urichess/chessboard/reader_zephyr/app/src/main2.c

/*
 * Copyright (c) 2017 Linaro Limited
 *
 * SPDX-License-Identifier: Apache-2.0
 */

#include <zephyr/kernel.h>
#include <zephyr/device.h>
#include <zephyr/drivers/gpio.h>
#include <zephyr/sys/printk.h>
#include <zephyr/sys/__assert.h>
#include <string.h>


#include <zephyr/devicetree.h>
#include <zephyr/drivers/adc.h>
#include <zephyr/sys/util.h>

/* size of stack area used by each thread */
#define STACKSIZE 1024

/* scheduling priority used by each thread */
#define PRIORITY 7

#define LED0_NODE DT_ALIAS(led0)

#if !DT_NODE_HAS_STATUS(LED0_NODE, okay)
#error "Unsupported board: led0 devicetree alias is not defined"
#endif


#if !DT_NODE_EXISTS(DT_PATH(zephyr_user)) || \
	!DT_NODE_HAS_PROP(DT_PATH(zephyr_user), io_channels) || \
	!DT_NODE_HAS_PROP(DT_PATH(zephyr_user), mux_gpios)
#error "Unsupported board: zephyr_user devicetree alias is not defined"
#endif

#define DT_SPEC_AND_COMMA(node_id, prop, idx) \
	ADC_DT_SPEC_GET_BY_IDX(node_id, idx),

/* Data of ADC io-channels specified in devicetree. */
static const struct adc_dt_spec adc_channels[] = {
	DT_FOREACH_PROP_ELEM(DT_PATH(zephyr_user), io_channels,
			     DT_SPEC_AND_COMMA)
};

#define DT_GPIO_SPEC_AND_COMMA(node_id, prop, idx) \
	GPIO_DT_SPEC_GET_BY_IDX(node_id, prop, idx),


static const struct gpio_dt_spec gpios_mux[] = {
	DT_FOREACH_PROP_ELEM(DT_PATH(zephyr_user), mux_gpios,
			     DT_GPIO_SPEC_AND_COMMA)
};




struct printk_data_t {
	void *fifo_reserved; /* 1st word reserved for use by fifo */
	uint32_t led;
	uint32_t cnt;
};

K_FIFO_DEFINE(printk_fifo);

struct led {
	struct gpio_dt_spec spec;
	uint8_t num;
};

static const struct led led0 = {
	.spec = GPIO_DT_SPEC_GET_OR(LED0_NODE, gpios, {0}),
	.num = 0,
};

void blink(const struct led *led, uint32_t sleep_ms, uint32_t id)
{
	const struct gpio_dt_spec *spec = &led->spec;
	int cnt = 0;
	int ret;

	if (!device_is_ready(spec->port)) {
		printk("Error: %s device is not ready\n", spec->port->name);
		return;
	}

	ret = gpio_pin_configure_dt(spec, GPIO_OUTPUT);
	if (ret != 0) {
		printk("Error %d: failed to configure pin %d (LED '%d')\n",
			ret, spec->pin, led->num);
		return;
	}

	while (1) {
		gpio_pin_set(spec->port, spec->pin, cnt % 2);

		struct printk_data_t tx_data = { .led = id, .cnt = cnt };

		size_t size = sizeof(struct printk_data_t);
		char *mem_ptr = k_malloc(size);
		__ASSERT_NO_MSG(mem_ptr != 0);

		memcpy(mem_ptr, &tx_data, size);

		k_fifo_put(&printk_fifo, mem_ptr);

		k_msleep(sleep_ms);
		cnt++;
	}
}

void blink0(void)
{
	blink(&led0, 1000, 0);
}

void uart_out(void)
{
	while (1) {
		struct printk_data_t *rx_data = k_fifo_get(&printk_fifo,
							   K_FOREVER);
		printk("Toggled led%d; counter=%d\n",
  		rx_data->led, rx_data->cnt);
		k_free(rx_data);
	}
}

K_THREAD_DEFINE(blink0_id, STACKSIZE, blink0, NULL, NULL, NULL,
		PRIORITY, 0, 0);
K_THREAD_DEFINE(uart_out_id, STACKSIZE, uart_out, NULL, NULL, NULL,
		PRIORITY, 0, 0);







int main(void)
{
	int ret;
	int err;
	uint32_t count = 0;
	uint16_t buf;
	struct adc_sequence sequence = {
		.buffer = &buf,
		/* buffer size in bytes, not number of samples */
		.buffer_size = sizeof(buf),
	};

	/* Configure channels individually prior to sampling. */
	for (size_t i = 0U; i < ARRAY_SIZE(adc_channels); i++) {
		if (!adc_is_ready_dt(&adc_channels[i])) {
			printk("ADC controller device %s not ready\n", adc_channels[i].dev->name);
			return 0;
		}

		err = adc_channel_setup_dt(&adc_channels[i]);
		if (err < 0) {
			printk("Could not setup channel #%d (%d)\n", i, err);
			return 0;
		}
	}

	/* Configure mux gpios */
	int muxsValue = 0;
	for (size_t nmux = 0U; nmux < ARRAY_SIZE(gpios_mux); nmux++)
	{
		const struct gpio_dt_spec *spec = &gpios_mux[nmux];
		if (!device_is_ready(spec->port)) {
			printk("Error: %s device is not ready\n", spec->port->name);
			return 0;
		}

		ret = gpio_pin_configure_dt(spec, GPIO_OUTPUT);
		if (ret != 0) {
			printk("Error %d: failed to configure gpioMux %d')\n",
				ret, nmux);
			return 0;
		}


		gpio_pin_set(spec->port, spec->pin, muxsValue);
	}
	printk("Initialized muxs to: %d\n", muxsValue);




#ifndef CONFIG_COVERAGE
	while (1) {
#else
	for (int k = 0; k < 10; k++) {
#endif
		printk("ADC reading[%u]:\n", count++);
		for (size_t i = 0U; i < ARRAY_SIZE(adc_channels); i++) {
			int32_t val_mv;

			printk("- %s, channel %d: ",
			       adc_channels[i].dev->name,
			       adc_channels[i].channel_id);

			(void)adc_sequence_init_dt(&adc_channels[i], &sequence);

			err = adc_read_dt(&adc_channels[i], &sequence);
			if (err < 0) {
				printk("Could not read (%d)\n", err);
				continue;
			}

			/*
			 * If using differential mode, the 16 bit value
			 * in the ADC sample buffer should be a signed 2's
			 * complement value.
			 */
			if (adc_channels[i].channel_cfg.differential) {
				val_mv = (int32_t)((int16_t)buf);
			} else {
				val_mv = (int32_t)buf;
			}
			printk("%"PRId32, val_mv);
			err = adc_raw_to_millivolts_dt(&adc_channels[i],
						       &val_mv);
			/* conversion to mV may not be supported, skip if not */
			if (err < 0) {
				printk(" (value in mV not available)\n");
			} else {
				printk(" = %"PRId32" mV\n", val_mv);
			}
		}

		muxsValue = muxsValue==0? 1:0;
		for (size_t nmux = 0U; nmux < ARRAY_SIZE(gpios_mux); nmux++)
		{
			const struct gpio_dt_spec *spec = &gpios_mux[nmux];
			gpio_pin_set(spec->port, spec->pin, muxsValue);

		}
		printk("Setting all muxs to: %d\n", muxsValue);


		k_sleep(K_MSEC(5000));
	}
	return 0;
}
